alangecker/sequi/software/src/date.cpp

// #include <Arduino.h>
#include "date.h"
#include "consts.h"

#if SOFTWAREI2C_ENABLE

#include <SoftwareWire.h> 
#include <RtcDS3231.h>
SoftwareWire myWire(SOFTWAREI2C_SDA, SOFTWAREI2C_SCL); 
RtcDS3231<SoftwareWire> Rtc(myWire);

#else

#include <Wire.h> 
#include <RtcDS3231.h>
RtcDS3231<TwoWire> Rtc(Wire);

#endif



#define countof(a) (sizeof(a) / sizeof(a[0]))


void printDateTime(const RtcDateTime& dt)
{
    char datestring[20];

    snprintf_P(datestring, 
            countof(datestring),
            PSTR("%04u-%02u-%02u %02u:%02u:%02u"),
            dt.Year(),
            dt.Month(),
            dt.Day(),
            dt.Hour(),
            dt.Minute(),
            dt.Second() );
    Serial.print(datestring);
}

void date_update(uint32_t secondsFrom2000) {
    Serial.println(secondsFrom2000);
    RtcDateTime time = RtcDateTime(secondsFrom2000);
    Serial.print("update time: ");
    printDateTime(time);
    Serial.println("");
    RtcDateTime now = Rtc.GetDateTime();
    if (now < time) {
        Rtc.SetDateTime(time);
    } else {
        Serial.println("provided time is older than compiled time. there must be an erro");
    }
}

void date_setup() {
  Serial.print("compiled: ");
  Serial.print(__DATE__);
  Serial.println(__TIME__);

  Rtc.Begin();
    RtcDateTime compiled = RtcDateTime(__DATE__, __TIME__);
    printDateTime(compiled);
    Serial.println();

    if (!Rtc.IsDateTimeValid()) 
    {
        if (Rtc.LastError() != 0)
        {
            // we have a communications error
            // see https://www.arduino.cc/en/Reference/WireEndTransmission for 
            // what the number means
            Serial.print("RTC communications error = ");
            Serial.println(Rtc.LastError());
        }
        else
        {
            // Common Causes:
            //    1) first time you ran and the device wasn't running yet
            //    2) the battery on the device is low or even missing

            Serial.println("RTC lost confidence in the DateTime!");

            // following line sets the RTC to the date & time this sketch was compiled
            // it will also reset the valid flag internally unless the Rtc device is
            // having an issue

            Rtc.SetDateTime(compiled);
        }
    }

    if (!Rtc.GetIsRunning())
    {
        Serial.println("RTC was not actively running, starting now");
        Rtc.SetIsRunning(true);
    }

    RtcDateTime now = Rtc.GetDateTime();
    if (now < compiled) 
    {
        Serial.println("RTC is older than compile time!  (Updating DateTime)");
        Rtc.SetDateTime(compiled);
    }
    else if (now > compiled) 
    {
        Serial.println("RTC is newer than compile time. (this is expected)");
    }
    else if (now == compiled) 
    {
        Serial.println("RTC is the same as compile time! (not expected but all is fine)");
    }
    
    // never assume the Rtc was last configured by you, so
    // just clear them to your needed state
    Rtc.Enable32kHzPin(false);
    Rtc.SetSquareWavePin(DS3231SquareWavePin_ModeNone); 

    // Rtc.SetDateTime(RtcDateTime(2018, 11, 31, 10, 59, 50));

}

RtcDateTime getDate() {
    if (!Rtc.IsDateTimeValid())  {
        if (Rtc.LastError() != 0)
        {
            // we have a communications error
            // see https://www.arduino.cc/en/Reference/WireEndTransmission for 
            // what the number means
            Serial.print("RTC communications error = ");
            Serial.println(Rtc.LastError());
        }
        else
        {
            // Common Causes:
            //    1) the battery on the device is low or even missing and the power line was disconnected
            Serial.println("RTC lost confidence in the DateTime!");
        }
    }
    // RtcDateTime now = Rtc.GetDateTime();
    // printDateTime(now);
    // RtcTemperature temp = Rtc.GetTemperature();
    // temp.Print(Serial);
    // Serial.println("");
    return Rtc.GetDateTime();
}
